dpaola2/Harmony/enclosure/mark-6/fit-rev-b/slicing/README.md

# Revision B prepared print plates

Print the wheel-check plate first. All plates use the A1, a 0.4 mm nozzle, PLA Basic and Textured PEI.

| Plate | Contents | Estimate |
| --- | --- | --- |
| [wheel-check](wheel-check/harmony-m6-b-wheel-check-a1.3mf) | Wheel coupon, four 14 mm spacers and pilot coupon | 27.4 minutes; 7.84 g |
| [shells](shells/harmony-m6-b-shells-a1.3mf) | Replacement tray and front | 98.1 minutes; 66.56 g |
| [retainers](retainers/harmony-m6-b-retainers-a1.3mf) | Two left and two right display retainers | 10.5 minutes; 0.8 g |

Print at 100% scale. Settings use 0.20 mm layers, four walls, 15% gyroid and no supports. The first plate has six objects.

The source STL hashes match the sliced inputs. Project G-code matches the standalone G-code. Mesh and deposited-path checks pass. Physical fit remains unverified.

Read the [assembly plan](../README.md) before assembling. The shells wait for the wheel test. Confirm loaded material and plate before printing. No printer job was sent.
