dpaola2/Harmony/PLAN.md

You can get *really* far on the software side before you ever touch a soldering iron or 3D printer, as long as you structure things right.

See `docs/README.md` for the documentation map and where to put gameplans vs. archives.

Given our MP3 player plan (ESP32, MicroPython, tactile buttons + small screen, Bluetooth audio out, iPod-style UI), here’s how I’d do it.

---

## Big idea: separate “brain” from “fingers”

Think in two layers:

1. **Core app logic (the “brain”)**

   * Knows:

     * What tracks exist
     * Which one is selected/playing
     * Current screen (Now Playing, Library, Settings, etc.)
     * How button presses change state
   * Doesn’t know:

     * What hardware it’s running on
     * Whether “up” came from a GPIO pin, a keyboard key, or a test

2. **Hardware layer (the “fingers”)**

   * Concrete implementations for:

     * Buttons
     * Screen
     * Storage (SD card / flash filesystem)
     * Audio/Bluetooth

If you design the core so it talks only to abstract interfaces (“give me button events”, “draw this text”), you can:

* Run everything on your laptop with **regular Python** and keyboard input.
* Write **unit tests** against the core.
* Only later write a MicroPython hardware adapter that plugs into the same interfaces.

---

## Phase 1 – Define your core interfaces & states

On your laptop, in a normal Python project:

1. **Define events**

   ```python
   from enum import Enum, auto

   class ButtonEvent(Enum):
       UP = auto()
       DOWN = auto()
       LEFT = auto()
       RIGHT = auto()
       SELECT = auto()
       BACK = auto()
       PLAY_PAUSE = auto()
   ```

2. **Define a minimal “screen” API**
   (this will be implemented differently on the laptop vs ESP32)

   ```python
   class Screen:
       def clear(self):
           raise NotImplementedError

       def draw_text(self, x: int, y: int, text: str):
           raise NotImplementedError

       def refresh(self):
           raise NotImplementedError
   ```

3. **Define a player model**

   ```python
   from dataclasses import dataclass

   @dataclass
   class Track:
       id: str
       title: str
       artist: str
       duration_secs: int
       path: str  # local file path

   @dataclass
   class PlayerState:
       tracks: list[Track]
       selected_index: int = 0
       playing_index: int | None = None
       is_playing: bool = False
       current_screen: str = "library"  # or "now_playing", "settings"
   ```

4. **Define core commands the hardware will call**

   ```python
   class PlayerApp:
       def __init__(self, state: PlayerState, screen: Screen):
           self.state = state
           self.screen = screen

       def handle_button(self, event: ButtonEvent):
           # purely state transitions; no GPIO, no Bluetooth here
           if self.state.current_screen == "library":
               self._handle_library_input(event)
           elif self.state.current_screen == "now_playing":
               self._handle_now_playing_input(event)
           self.render()

       def render(self):
           # draw the current UI to the screen abstraction
           self.screen.clear()
           if self.state.current_screen == "library":
               self._render_library()
           elif self.state.current_screen == "now_playing":
               self._render_now_playing()
           self.screen.refresh()
   ```

All of this is **100% portable** between your laptop and the ESP32.

---

## Phase 2 – Build a PC “simulator” (your first working app)

Now you make a fake hardware layer that runs on your laptop:

1. **Text-based screen implementation**
   Example: use `curses` or just simple print-based rendering.

   ```python
   import os

   class ConsoleScreen(Screen):
       def clear(self):
           os.system("clear")

       def draw_text(self, x: int, y: int, text: str):
           # simplest version: ignore x,y and just print lines
           print(text)

       def refresh(self):
           pass
   ```

2. **Keyboard → button events**

   * For a quick prototype, just read input from the keyboard in a loop:

     ```python
     key_map = {
         "w": ButtonEvent.UP,
         "s": ButtonEvent.DOWN,
         "a": ButtonEvent.LEFT,
         "d": ButtonEvent.RIGHT,
         " ": ButtonEvent.SELECT,
         "p": ButtonEvent.PLAY_PAUSE,
         "q": ButtonEvent.BACK,
     }
     ```

3. **Run loop**

   ```python
   def main():
       tracks = [
           Track("1", "Song One", "Artist A", 180, "/music/song1.mp3"),
           Track("2", "Song Two", "Artist B", 200, "/music/song2.mp3"),
       ]
       state = PlayerState(tracks=tracks)
       screen = ConsoleScreen()
       app = PlayerApp(state, screen)

       app.render()
       while True:
           key = input("Key (w/s/a/d/space/p/q): ").strip()
           if key == "x":
               break
           event = key_map.get(key)
           if event:
               app.handle_button(event)

   if __name__ == "__main__":
       main()
   ```

At this point you’ll have:

* A working “MP3 player” UI on your laptop
* Library navigation
* Now Playing screen
* Play/pause state machine (even if audio is stubbed)

---

## Phase 3 – Add tests around the core

Now that your logic is decoupled, you can test it like a normal app:

1. **Install pytest** and write tests:

   ```python
   def test_down_moves_selection():
       tracks = [Track(str(i), f"Song {i}", "Artist", 120, "") for i in range(3)]
       state = PlayerState(tracks=tracks)
       screen = DummyScreen()  # no-op implementation

       app = PlayerApp(state, screen)
       app.handle_button(ButtonEvent.DOWN)
       assert app.state.selected_index == 1
   ```

2. Test scenarios like:

   * Pressing PLAY on Library → sets `playing_index` and `is_playing = True`
   * Pressing PLAY on Now Playing toggles pause
   * Reaching end of list wraps or stops (decide behavior)
   * BACK from Now Playing returns you to Library

These tests are the safety net you’ll keep using when you later port to MicroPython.

---

## Phase 4 – Decide how “real” audio works

You can keep audio out of the core and treat it as a **service**:

```python
class AudioBackend:
    def play(self, track: Track): ...
    def pause(self): ...
    def resume(self): ...
    def stop(self): ...
```

* In your **PC simulator**, `AudioBackend` could:

  * Actually play MP3s using a Python library, **or**
  * Just print what it *would* do (“Playing Song One”).
* On the **ESP32**, `AudioBackend` becomes:

  * A MicroPython module that:

    * Reads from SD card/flash
    * Sends PCM over I2S to a DAC/headphone amp **or**
    * Streams via Bluetooth A2DP (harder but doable in C/ESP-IDF; MicroPython options are more limited).

Your core `PlayerApp` just calls:

```python
def _play_selected_track(self):
    track = self.state.tracks[self.state.selected_index]
    self.audio_backend.play(track)
    self.state.playing_index = self.state.selected_index
    self.state.is_playing = True
```

---

## Phase 5 – Only then worry about actual hardware

When your laptop simulator feels good and tests are passing, *then* you start working with an ESP32 dev board:

1. **Pick an ESP32 dev board + display** (this was in our other chat).
2. **Port the core to MicroPython**:

   * Most of your Python code will just work.
   * You might have to trim things for memory and avoid heavy libraries.
3. **Implement MicroPython versions of your interfaces**:

   * `EspScreen` using your actual display driver.
   * `EspButtons` that reads GPIOs and maps them to `ButtonEvent`s.
   * `EspAudioBackend` that hooks into whatever audio path you choose.

Because the interfaces are already defined, this becomes “just wiring”:

```python
# micropython_main.py
from core import PlayerApp, PlayerState, Track, ButtonEvent
from esp_screen import EspScreen
from esp_buttons import read_button_event
from esp_audio import EspAudioBackend

def main():
    tracks = load_tracks_from_fs()  # same idea as on PC
    state = PlayerState(tracks=tracks)
    screen = EspScreen()
    audio = EspAudioBackend()
    app = PlayerApp(state, screen, audio_backend=audio)

    app.render()
    while True:
        event = read_button_event()
        if event:
            app.handle_button(event)
```

You’ll still test logic changes on your PC first, run pytest, then deploy to the ESP32 dev board to verify hardware behavior.

---

## Phase 6 – Only *after* that: custom PCB + 3D case

Once:

* The app feels good in the simulator
* The ESP32 dev board version works reliably
* You’re comfortable with button layout and screen usage

**Then** you:

* Lock in hardware choices (exact ESP32 module, DAC, amp, battery management).
* Design PCB + mechanical layout.
* Design and 3D-print the case around that.

At that point you’re mostly doing **mechanical integration**, not discovering fundamental UI or software architecture issues.

---

## If you want, next step

If you’d like, I can:

* Turn this into a **repo structure** (folder layout, file names, `core/`, `platform/pc/`, `platform/esp32/`, etc.), and
* Sketch a minimal but real `PlayerApp` and a couple of pytest tests you could literally drop into a new project.
