dpaola2/Harmony/enclosure/harmony-r1/preview/exploded.png

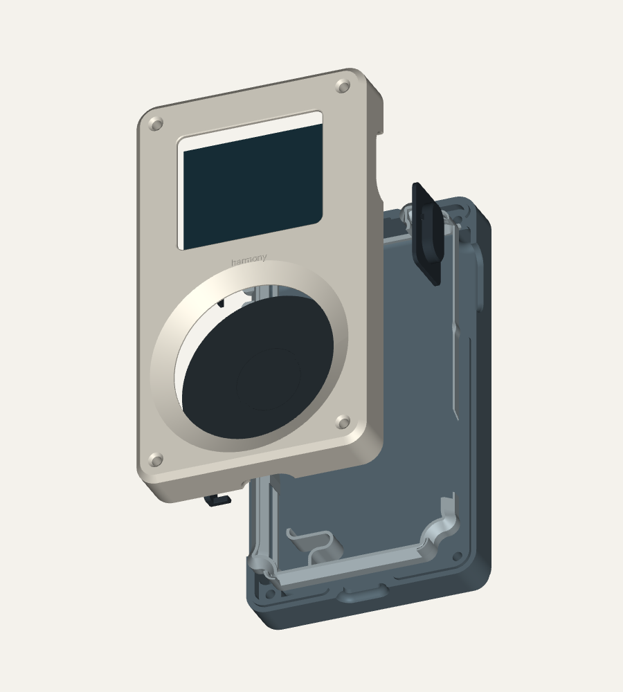
enclosure/harmony-r1/preview/exploded.png
