dpaola2/Harmony/enclosure/harmony-r2-globtek/preview/globtek-fit.png

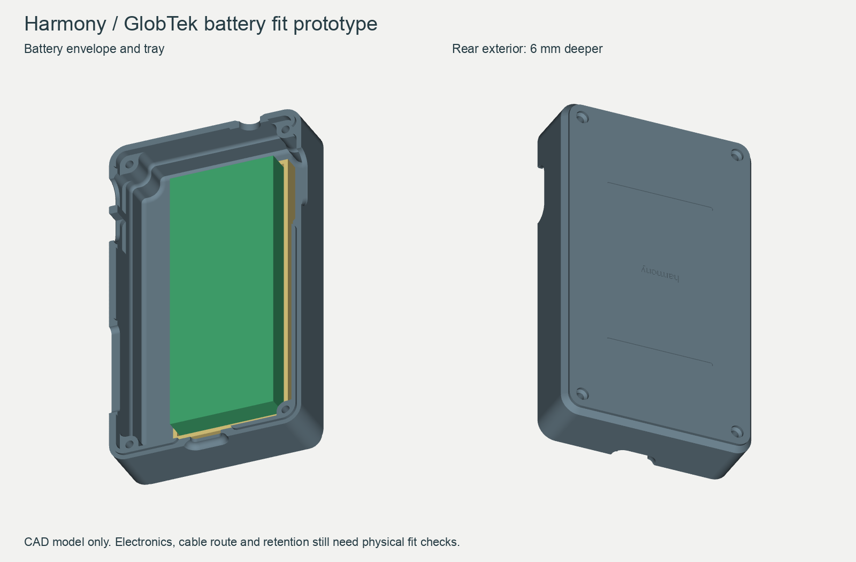
enclosure/harmony-r2-globtek/preview/globtek-fit.png
