dpaola2/Harmony/enclosure/harmony-r2-globtek/preview/inside.png

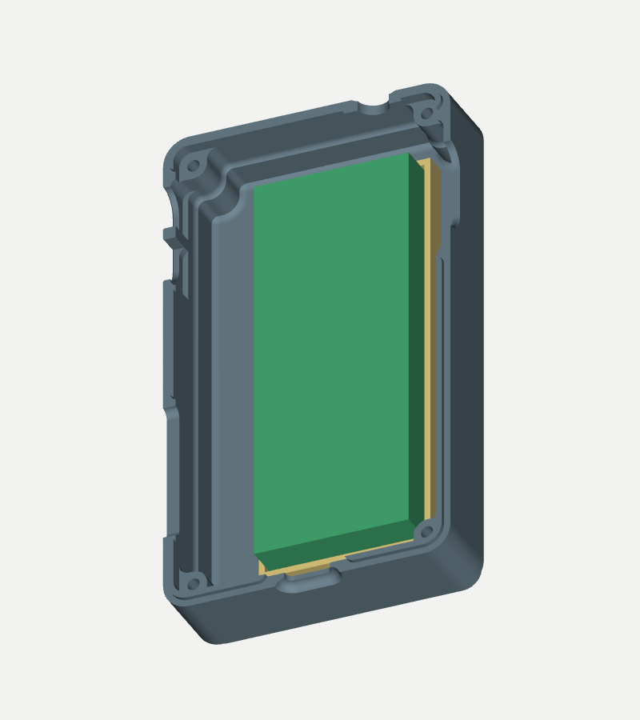
enclosure/harmony-r2-globtek/preview/inside.png
