dpaola2/Harmony/enclosure/harmony-r2-globtek/preview/outside.png

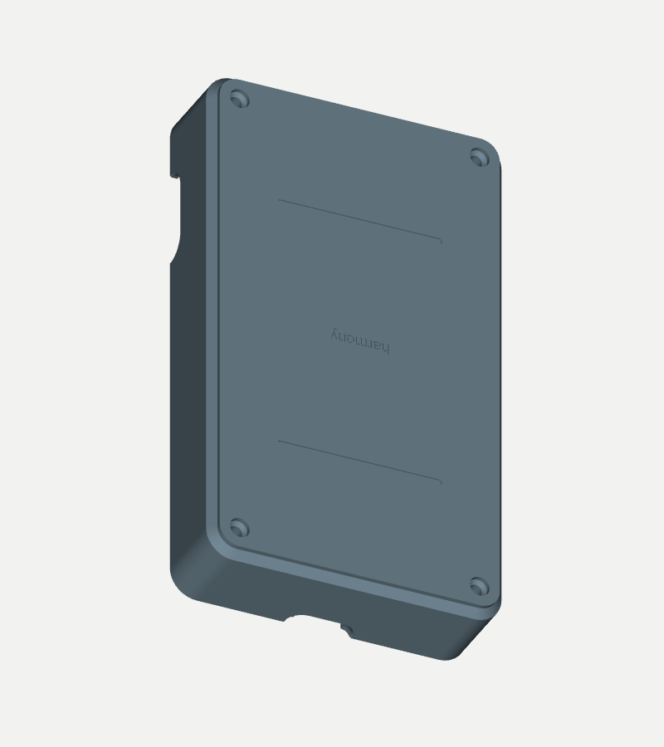
enclosure/harmony-r2-globtek/preview/outside.png
