dpaola2/Harmony/enclosure/mark-6/fit-prototype/preview/hollow-fit.png

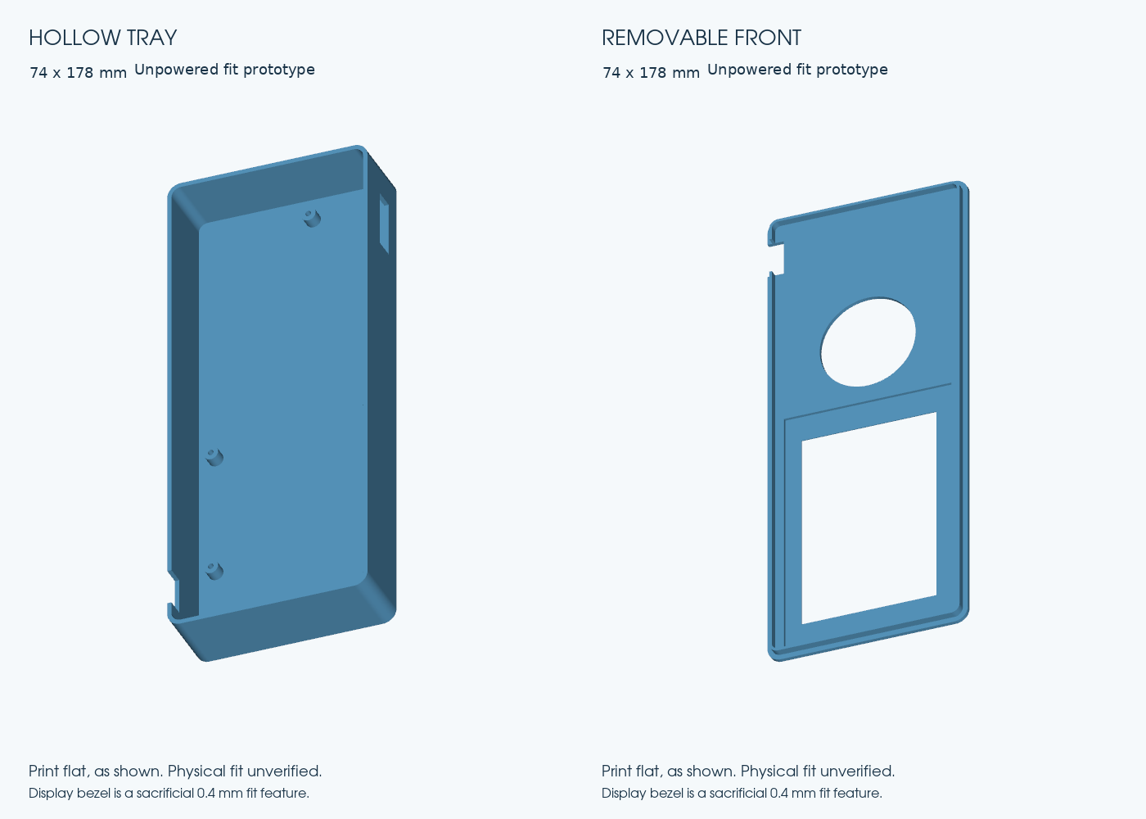
enclosure/mark-6/fit-prototype/preview/hollow-fit.png
