dpaola2/Harmony/enclosure/mark-6/fit-rev-b/slicing/retainers/toolpath-review.png

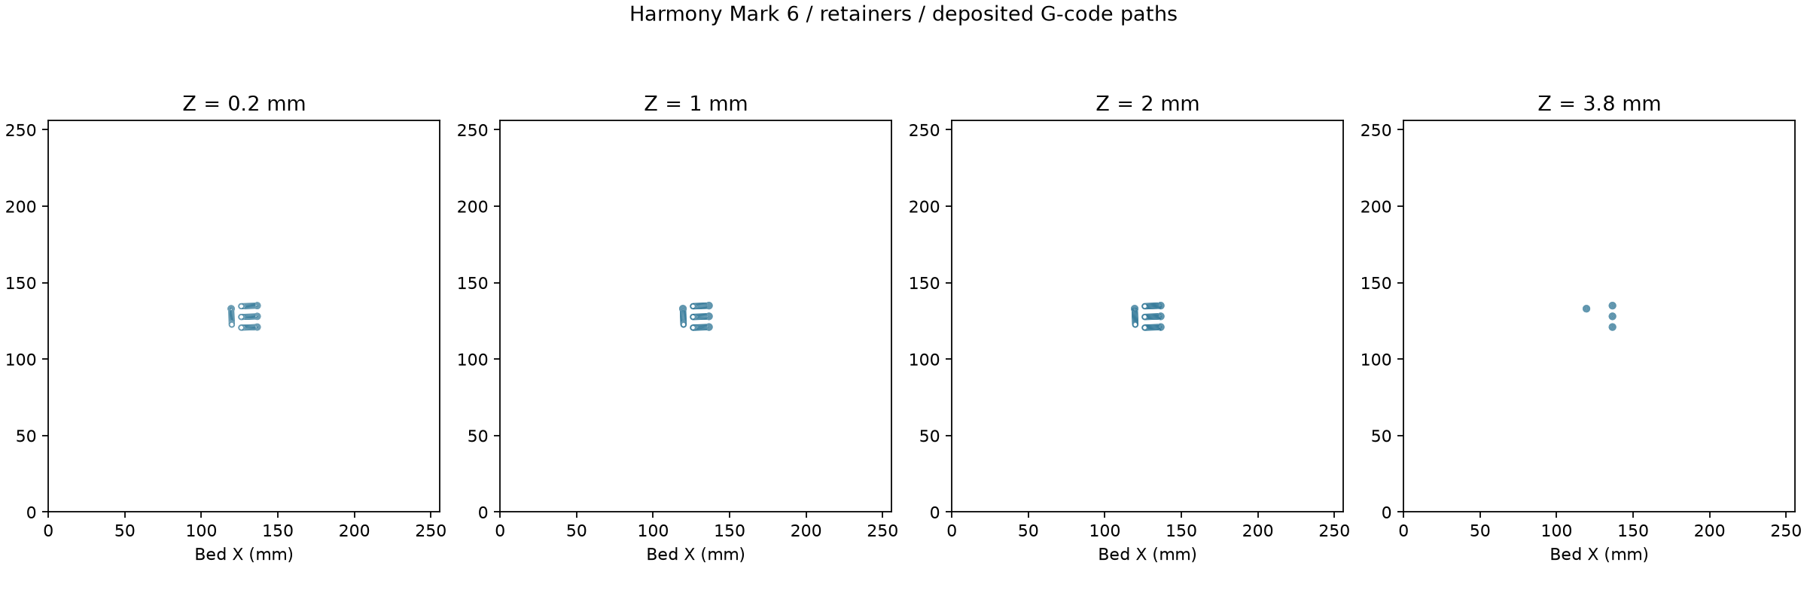
enclosure/mark-6/fit-rev-b/slicing/retainers/toolpath-review.png
