dpaola2/Harmony/enclosure/mark-6/fit-rev-b/slicing/shells/toolpath-review.png

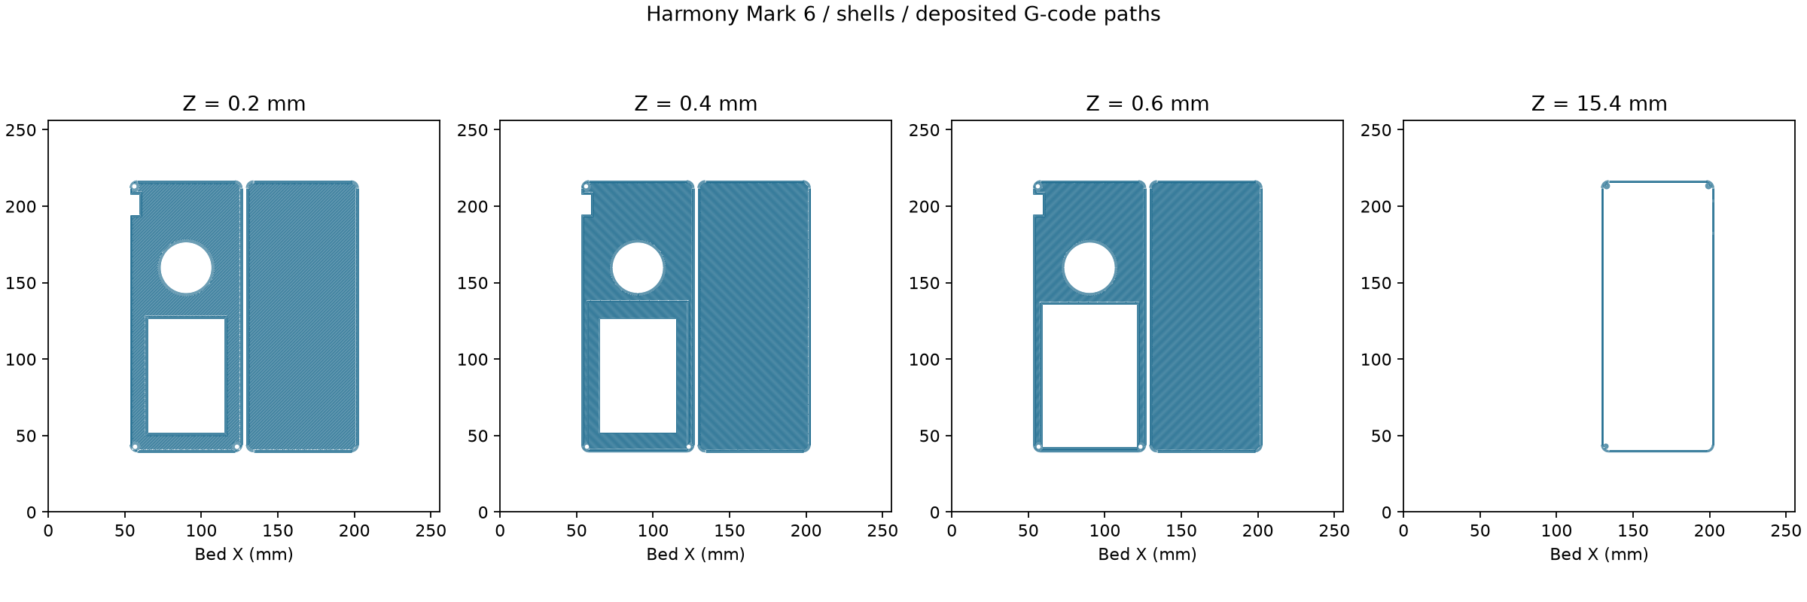
enclosure/mark-6/fit-rev-b/slicing/shells/toolpath-review.png
