dpaola2/Harmony/enclosure/mark-6/size-mockup/preview/size-mockup.png

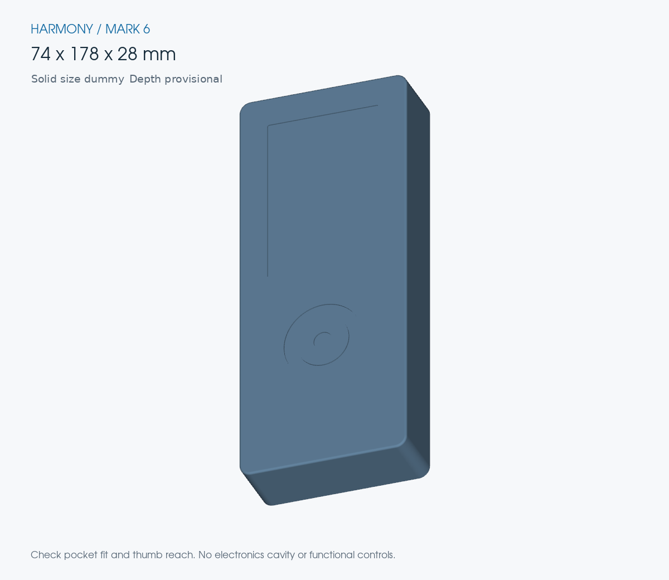
enclosure/mark-6/size-mockup/preview/size-mockup.png
