dpaola2/Harmony/hardware/mark-7/inventory-20260928/README.md

# September 28 Mark-7 inventory evidence

Dave supplied these original photographs during scope definition.

- `IMG_7727.HEIC`: GlobTek BL2200F9031781S1PCKT, 3.7 V, 2200 mAh, 8.14 Wh. Label assigns red positive, white NTC and black negative. Connector voltage and polarity remain unmeasured.
- `IMG_7730.HEIC`: ELEGOO Double Sided PCB Kit packaging. It advertises plated holes, five board sizes and 1.6 mm FR4. The contents, exact dimensions and pad connectivity remain unmeasured.

Dave reports ample wire, a multimeter and a soldering iron. He reports purchasing Adafruit #4046, #261 and #4559. These statements establish inventory and purchase intent/results, not an assembled or electrically verified adapter.

Original file checksums are in `sha256.json`. See [portable scope](../../../docs/mark-7-portable-scope.md) and [Mark-6 lessons](../../../docs/mark-6-lessons-and-portable-next-step.md). Build Mark-7 portable Bluetooth player (HARMONY-19) owns follow-up work.
