dpaola2/Harmony/hardware/mark-6/carrier-rev-a/output/supplier-quote/supplier-request-draft.md

# Mark 6 supplier request draft

Prepared September 26, 2026. Unsent. Proposed recipient: service@pcbway.com.
Attachment: `harmony-mark6-rev-a-supplier-quote.zip`.

Subject: DFM review and turnkey quote: Harmony Mark 6 carrier, Rev A

Hello,

Please quote fabrication and complete assembly of the attached four-layer carrier. Please price one, two and five assembled carriers separately. Your website lists a five-piece minimum. If that applies here, please distinguish the minimum bare-board quantity from the minimum assembled quantity.

Each carrier has 36 installed components: 34 SMT parts and two through-hole Samtec sockets. Please source the exact BOM and install both sockets. The customer must receive a carrier that requires no soldering. External processor, display and control modules are outside this quote.

The board needs 1.6 mm FR-4, ENIG and resin-filled, copper-capped vias at the nine listed locations. Please preserve the antenna cutout and copper exclusion. The package includes fabrication details and connector constraints.

Please return the DFM findings, BOM availability, proposed stackup, panel drawing and placement preview. Review U1's stencil and thermal holes, socket tail tolerances, and connector orientation. Identify substitutions for approval before using them.

Please itemize boards, components, assembly, tooling, testing and shipping to the United States. Include minimum component quantities, unused-part policy, lead time, quote validity and tax or duty assumptions. State any holiday effect on the schedule.

This request is for review and pricing only. Please wait for written production release before fabrication or assembly. Header mating, ribbon mapping and powered qualification remain open.

Thank you,
Dave
