dpaola2/Harmony/enclosure/mark-6/fit-prototype/cad/ano-spacer-12mm.step

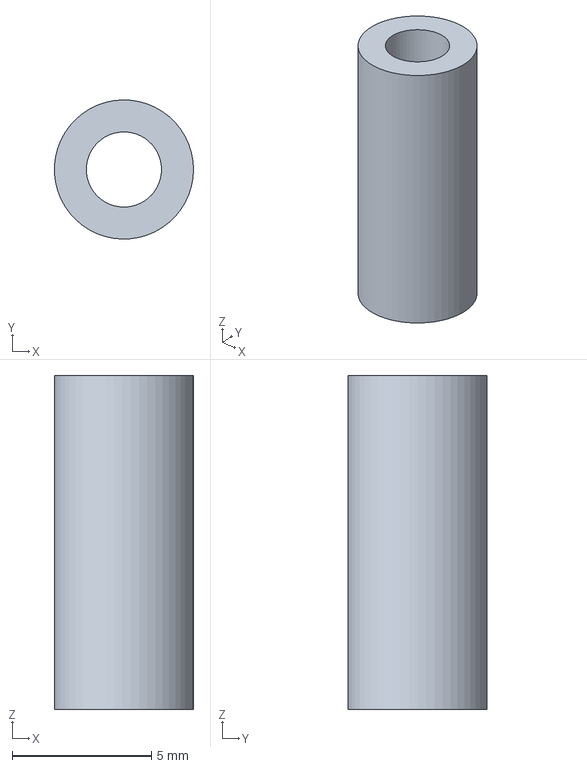
[picture p33: CAD file, 2026-09-25]
enclosure/mark-6/fit-prototype/cad/ano-spacer-12mm.step
5.00 x 5.00 x 12.0 mm
