dpaola2/Harmony/enclosure/mark-6/fit-prototype/slicing/gauges/harmony-mark6-gauges-a1.3mf

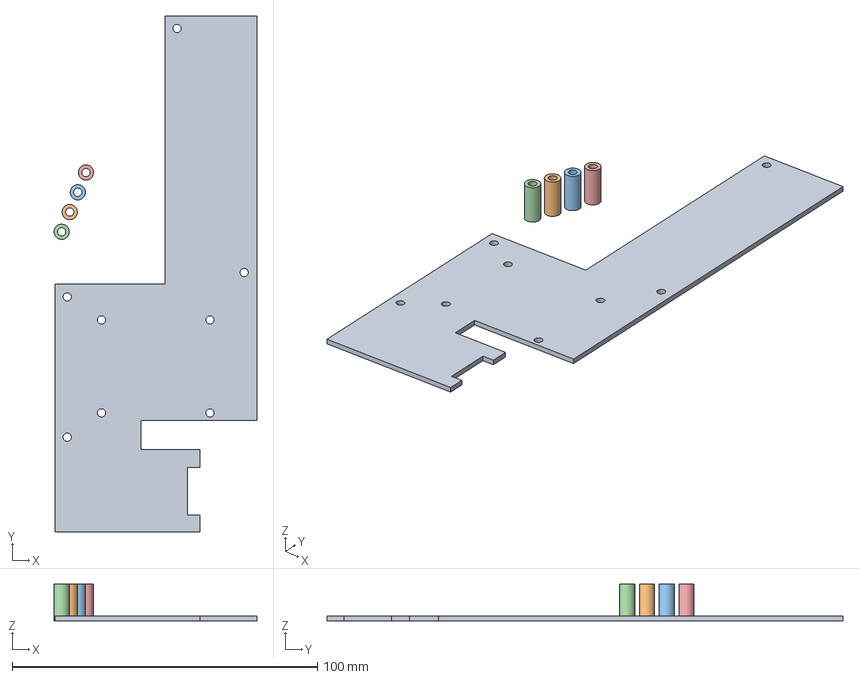
[picture p34: CAD file, 2026-09-25]
enclosure/mark-6/fit-prototype/slicing/gauges/harmony-mark6-gauges-a1.3mf
66.5 x 169.0 x 12.0 mm
harmony-mark6-carrier-gauge.stl
harmony-mark6-ano-spacer-12mm.stl_1
harmony-mark6-ano-spacer-12mm.stl_2
harmony-mark6-ano-spacer-12mm.stl_3
harmony-mark6-ano-spacer-12mm.stl_4
