dpaola2/Harmony/enclosure/mark-6/fit-prototype/slicing/shells/harmony-mark6-shells-a1.3mf

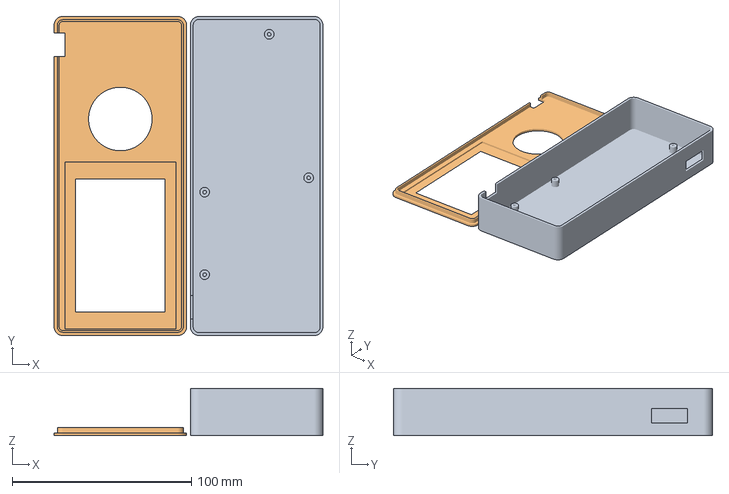
[picture p35: CAD file, 2026-09-25]
enclosure/mark-6/fit-prototype/slicing/shells/harmony-mark6-shells-a1.3mf
150.0 x 178.0 x 26.4 mm
harmony-mark6-tray.stl
harmony-mark6-front.stl
