dpaola2/Harmony/enclosure/mark-6/fit-rev-b/slicing/retainers/harmony-m6-b-retainers-a1.3mf

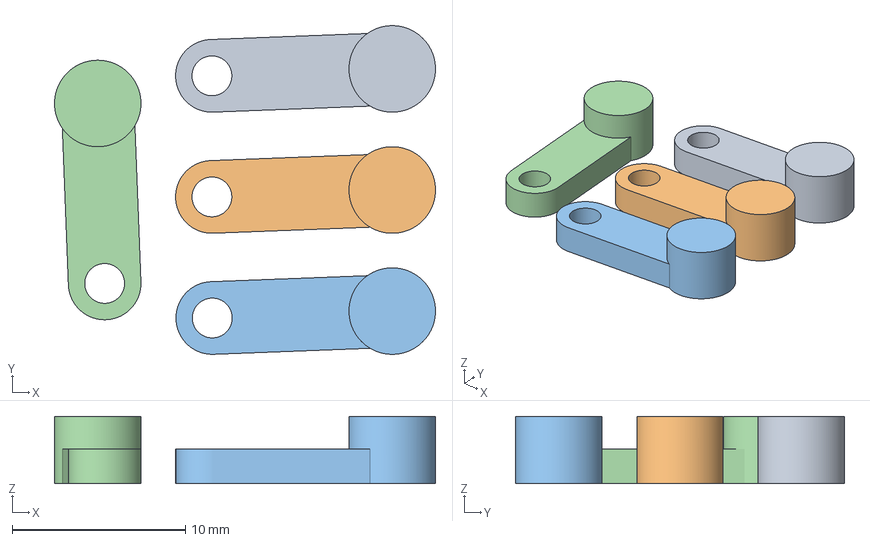
[picture p36: CAD file, 2026-09-26]
enclosure/mark-6/fit-rev-b/slicing/retainers/harmony-m6-b-retainers-a1.3mf
22.0 x 19.0 x 3.90 mm
harmony-m6-b-display-retainer-left.stl_1
harmony-m6-b-display-retainer-left.stl_2
harmony-m6-b-display-retainer-right.stl_1
harmony-m6-b-display-retainer-right.stl_2
