dpaola2/Harmony/enclosure/mark-6/fit-rev-b/slicing/shells/harmony-m6-b-shells-a1.3mf

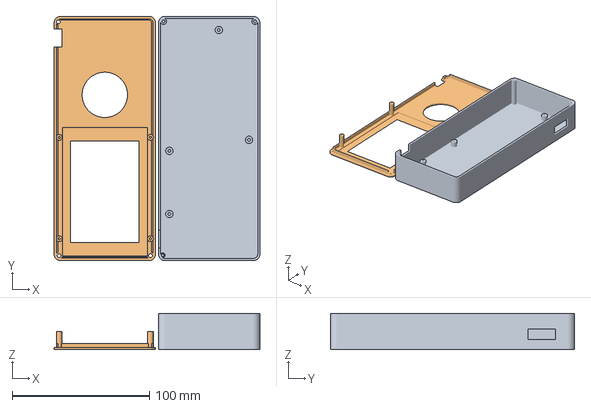
[picture p37: CAD file, 2026-09-26]
enclosure/mark-6/fit-rev-b/slicing/shells/harmony-m6-b-shells-a1.3mf
150.0 x 178.0 x 26.4 mm
harmony-m6-b-tray.stl
harmony-m6-b-front.stl
