dpaola2/Harmony/enclosure/mark-6/fit-rev-b/slicing/wheel-check/harmony-m6-b-wheel-check-a1.3mf

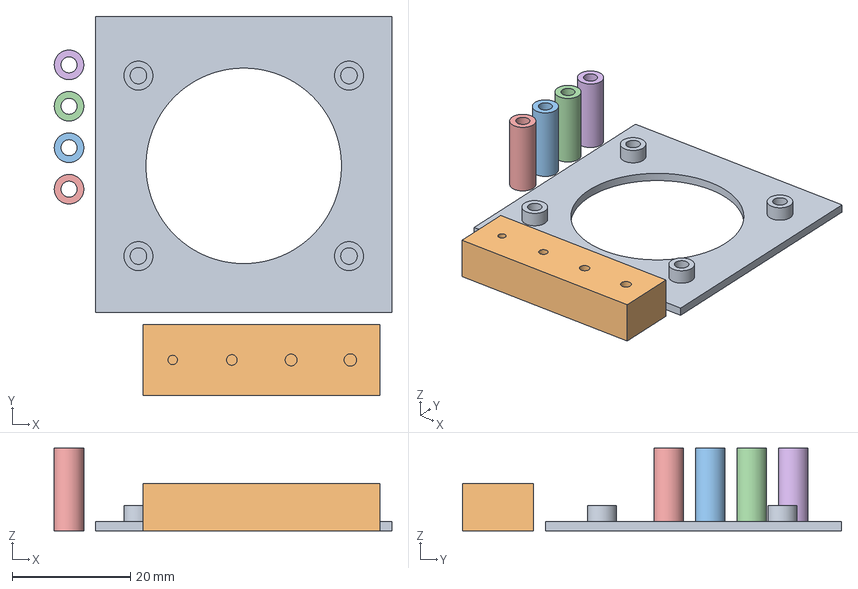
[picture p38: CAD file, 2026-09-26]
enclosure/mark-6/fit-rev-b/slicing/wheel-check/harmony-m6-b-wheel-check-a1.3mf
57.0 x 64.0 x 14.0 mm
harmony-m6-b-wheel-coupon.stl
harmony-m6-b-pilot-coupon.stl
harmony-m6-b-ano-spacer-14mm.stl_1
harmony-m6-b-ano-spacer-14mm.stl_2
harmony-m6-b-ano-spacer-14mm.stl_3
harmony-m6-b-ano-spacer-14mm.stl_4
