dpaola2/Harmony/enclosure/mark-6/size-mockup/cad/harmony-mark6-size.step

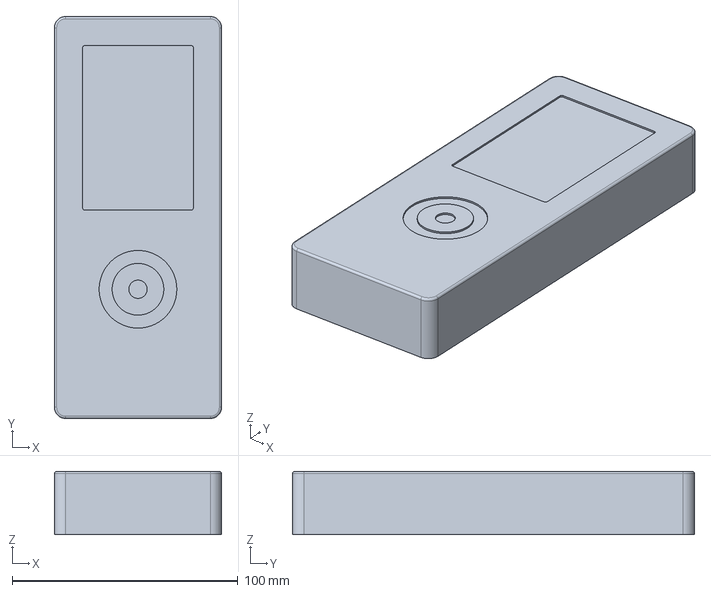
[picture p39: CAD file, 2026-09-25]
enclosure/mark-6/size-mockup/cad/harmony-mark6-size.step
74.0 x 178.0 x 28.0 mm
