dpaola2/Harmony/enclosure/harmony-r1/cad/battery-envelope-reference.step

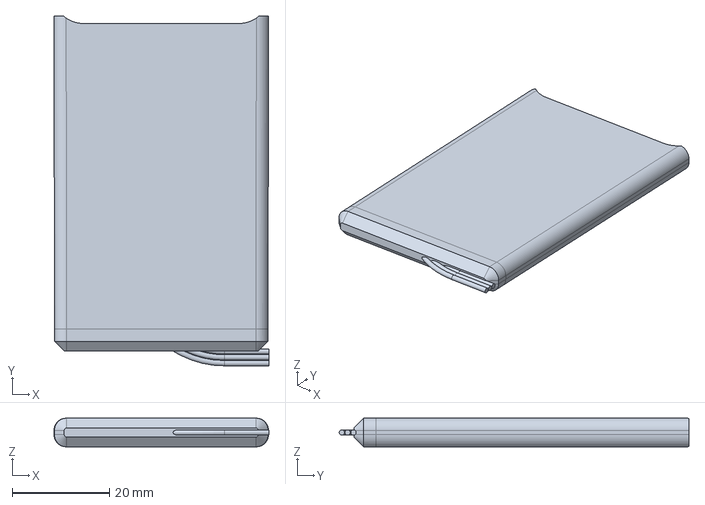
[picture p40: CAD file, 2026-09-20]
enclosure/harmony-r1/cad/battery-envelope-reference.step
44.3 x 72.1 x 5.90 mm
