dpaola2/Harmony/enclosure/harmony-r1/print/harmony-fit-test.3mf

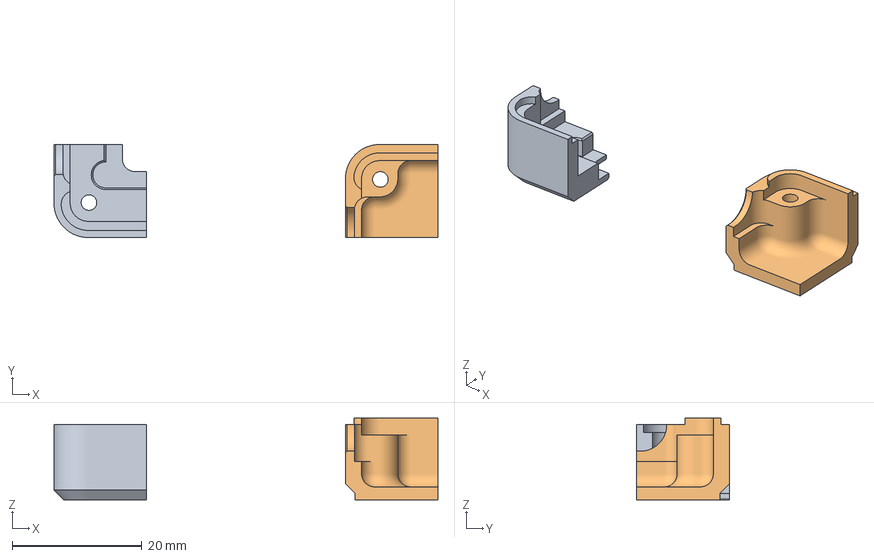
[picture p41: CAD file, 2026-09-20]
enclosure/harmony-r1/print/harmony-fit-test.3mf
59.3 x 14.4 x 12.6 mm
fit-front
fit-back
