dpaola2/Harmony/enclosure/harmony-r1/source/Case.FCStd

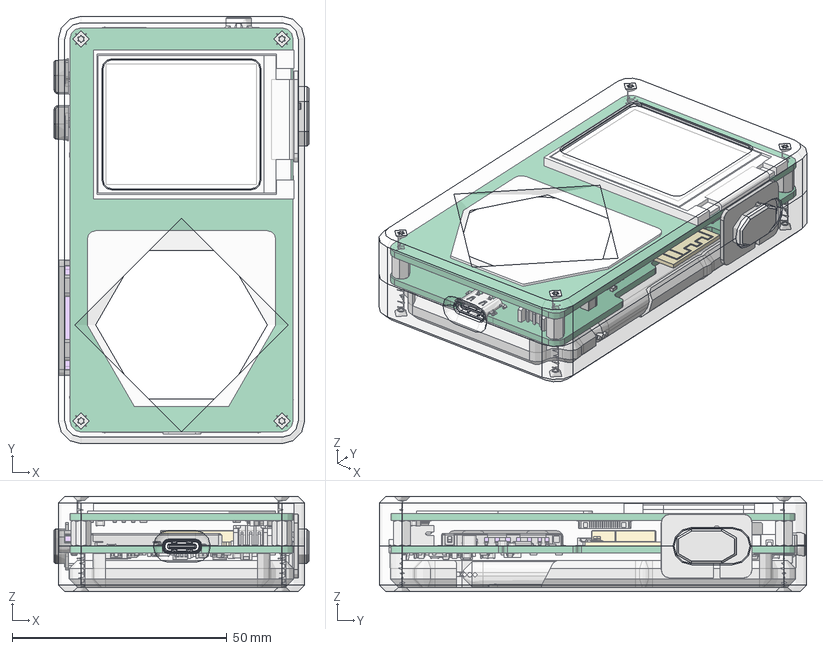
[picture p42: CAD file, 2026-09-20]
enclosure/harmony-r1/source/Case.FCStd
59.4 x 99.6 x 22.2 mm
Back
Pcb_d9b2
${REFERENCE}_TSOT_23_null
${REFERENCE}_SOT_23_5_null
${REFERENCE}_L_1008_2520Metric_null x 2
${REFERENCE}_R_0805_2012Metric_null x 4
${REFERENCE}_C_0805_2012Metric_null x 16
${REFERENCE}_R_0603_1608Metric_null x 28
${REFERENCE}_QFN-20-1EP_4x4mm_Pitch0.5mm_null
${REFERENCE}_C_0603_1608Metric_null x 11
${REFERENCE}_HVQFN_24_1EP_4x4mm_P05mm_EP21x21mm_null
${REFERENCE}_SOT_23_null
${REFERENCE}_SOT_323_SC_70_null x 2
REF_WSON-10-1EP_2.5x2.5mm_P0.5mm_EP1.2x2mm_null
${REFERENCE}_SOT_23_6_null
${REFERENCE}_C_1206_3216Metric_null x 3
${REFERENCE}_SSOP_20_44x65mm_P065mm_null
${REFERENCE}_TQFP_32_7x7mm_P08mm_null
U7_WSON8_4x4mm_Pitch08mm_null
PCB Edge_usb4510-03-1-a_null
${REFERENCE}_L_0603_1608Metric_null
${REFERENCE}_JST_S3B_PH_K_null
J2_5052781533_null
${REFERENCE}_TSSOP_16_44x5mm_P065mm_null
${REFERENCE}_microSD_HC_Hirose_DM3D-SF_null[2]
${REFERENCE}_DM1AA-SF-PEJ v2_null[3]
PCB EDGE_EVQ-P4HB3B--3DModel-STEP-56544_null x 2
U15_ESP32-WROVER-I--3DModel-STEP-56544_null[2]
${REFERENCE}_JS102011SAQN v2_null
${REFERENCE}_C_1210_3225Metric_null
PCB EDGE_SJ-3506-SMT_null
Pcb_8c068
${REFERENCE}_R_0603_1608Metric_null028 x 9
${REFERENCE}_C_0805_2012Metric_null016 x 3
${REFERENCE}_C_1206_3216Metric_null003
J4_5052781533_null
${REFERENCE}_VSSOP_10_3x3mm_P05mm_null
${REFERENCE}_C_0603_1608Metric_null011
${REFERENCE}_SOT_323_SC_70_null002
Touchpad (Smaller)
Display (ER-TFT018-2)
Wurth 970060244 (Top Left)
Wurth 970060244 (Top Right)
Wurth 970060244 (Bottom Left)
Wurth 970060244 (Bottom Right)
474283-SHK-M2-8-V2-A2 (Top Left)
474283-SHK-M2-8-V2-A2 (Top Right)
474283-SHK-M2-8-V2-A2 (Bottom Left)
474283-SHK-M2-8-V2-A2 (Bottom Right)
474289-SHK-M2-8-V2-A2 (Top Left)
474289-SHK-M2-8-V2-A2 (Top Right)
474289-SHK-M2-8-V2-A2 (Bottom Left)
474289-SHK-M2-8-V2-A2 (Bottom Right)
SD Card Blank
Battery (Batch 0, Smaller)
Battery (Batch 1, Larger)
Button1
Button2
Switch
SD Caddy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
