dpaola2/Harmony/enclosure/harmony-r2-globtek/print/battery-dummy.stl

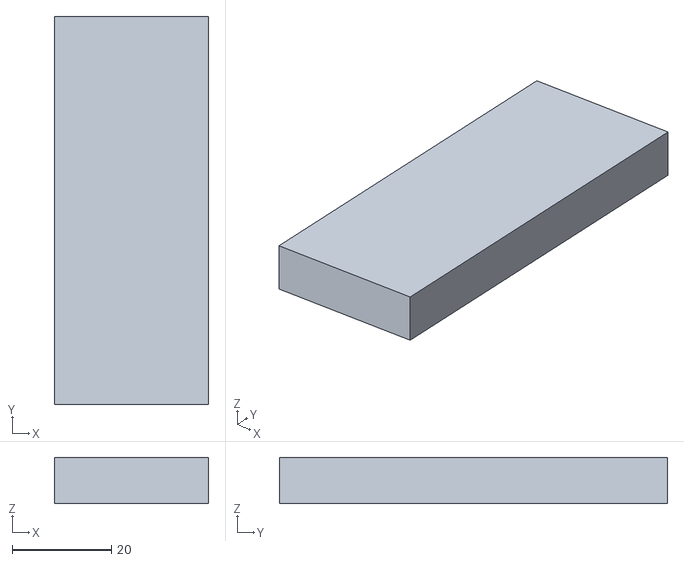
[picture p43: CAD file, 2026-09-20]
enclosure/harmony-r2-globtek/print/battery-dummy.stl
31.0 x 78.0 x 9.30
