dpaola2/Harmony/enclosure/mark-6/fit-prototype/print/harmony-mark6-front.3mf

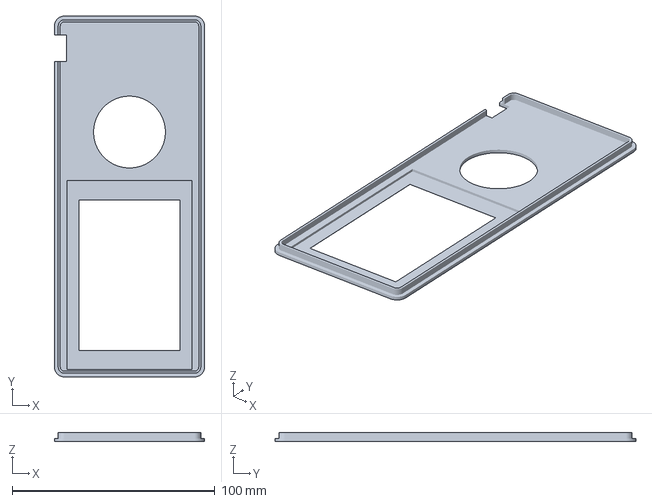
[picture p44: CAD file, 2026-09-25]
enclosure/mark-6/fit-prototype/print/harmony-mark6-front.3mf
74.0 x 178.0 x 4.60 mm
