dpaola2/Harmony/enclosure/mark-6/fit-rev-b/print/harmony-m6-b-pilot-coupon.3mf

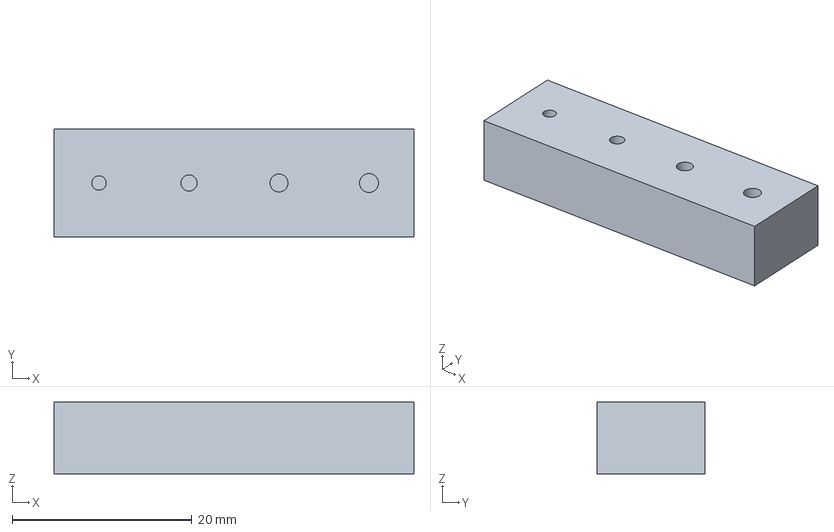
[picture p45: CAD file, 2026-09-26]
enclosure/mark-6/fit-rev-b/print/harmony-m6-b-pilot-coupon.3mf
40.0 x 12.0 x 8.00 mm
