dpaola2/Harmony/enclosure/harmony-r1/cad/display-lens-reference.step

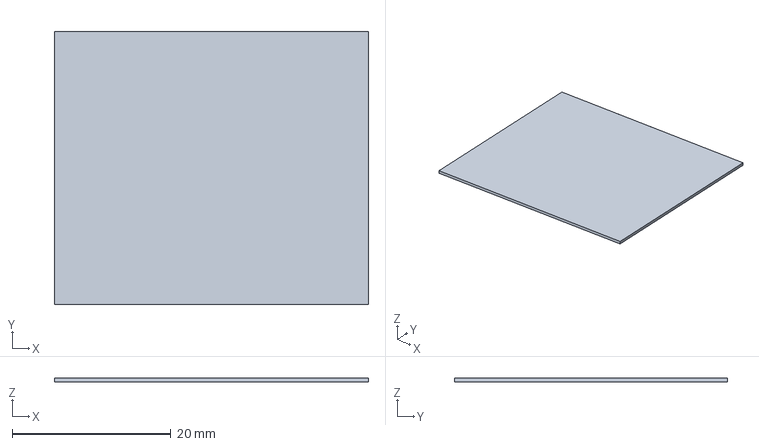
[picture p46: CAD file, 2026-09-20]
enclosure/harmony-r1/cad/display-lens-reference.step
39.6 x 34.4 x 0.5 mm
