dpaola2/Harmony/enclosure/harmony-r1/print/harmony-small-parts.3mf

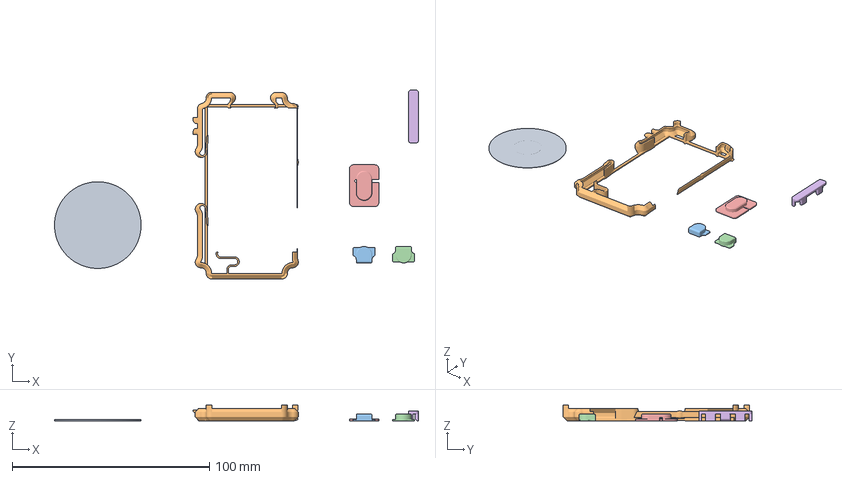
[picture p47: CAD file, 2026-09-20]
enclosure/harmony-r1/print/harmony-small-parts.3mf
184.5 x 95.8 x 7.90 mm
touch-cover
battery-cage
button-upper
button-lower
hold-switch
sd-caddy
