dpaola2/Harmony/enclosure/harmony-r2-globtek/cad/battery-clearance-envelope.step

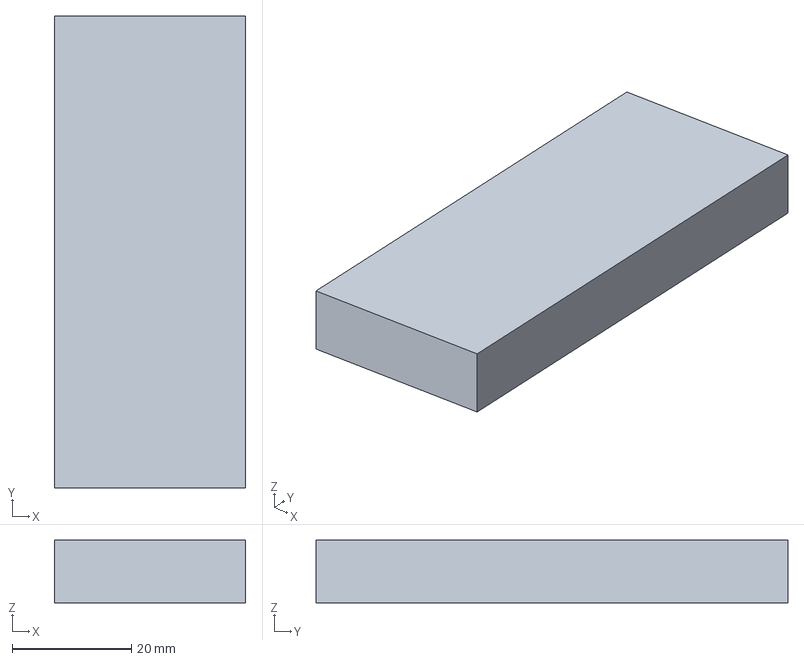
[picture p48: CAD file, 2026-09-20]
enclosure/harmony-r2-globtek/cad/battery-clearance-envelope.step
32.0 x 79.0 x 10.5 mm
