dpaola2/Harmony/enclosure/mark-6/fit-rev-b/cad/ano-spacer-14mm.step

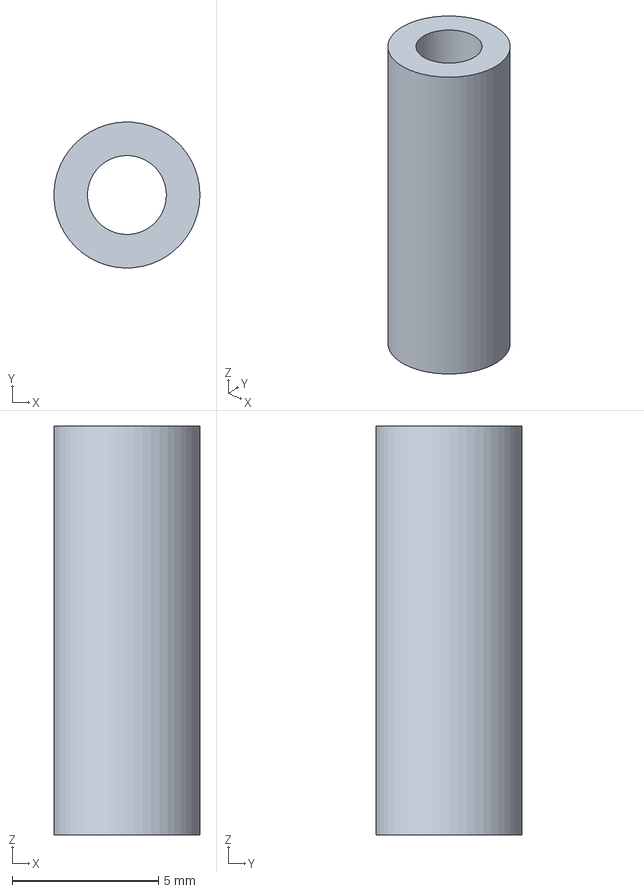
[picture p49: CAD file, 2026-09-26]
enclosure/mark-6/fit-rev-b/cad/ano-spacer-14mm.step
5.00 x 5.00 x 14.0 mm
