dpaola2/Harmony/enclosure/mark-6/fit-rev-b/print/harmony-m6-b-wheel-coupon.3mf

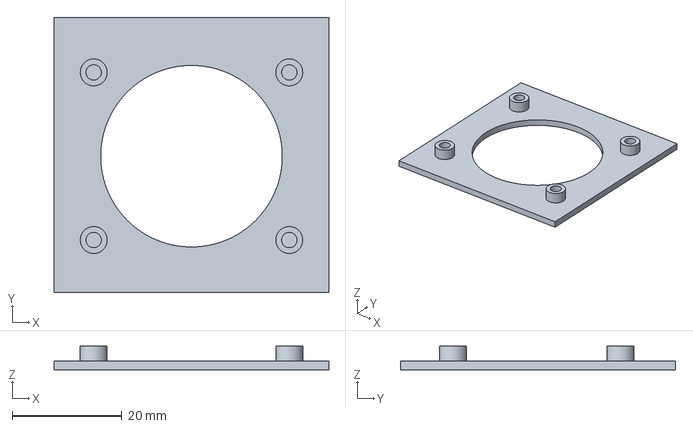
[picture p50: CAD file, 2026-09-26]
enclosure/mark-6/fit-rev-b/print/harmony-m6-b-wheel-coupon.3mf
50.0 x 50.0 x 4.33 mm
