dpaola2/Harmony/enclosure/harmony-r2-globtek/cad/back.step

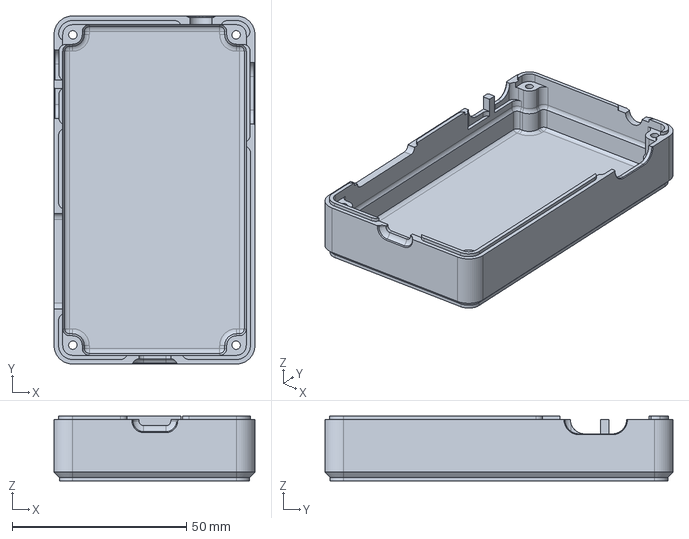
[picture p51: CAD file, 2026-09-20]
enclosure/harmony-r2-globtek/cad/back.step
57.6 x 99.8 x 18.6 mm
