dpaola2/Harmony/enclosure/harmony-r1/cad/battery-cage.step

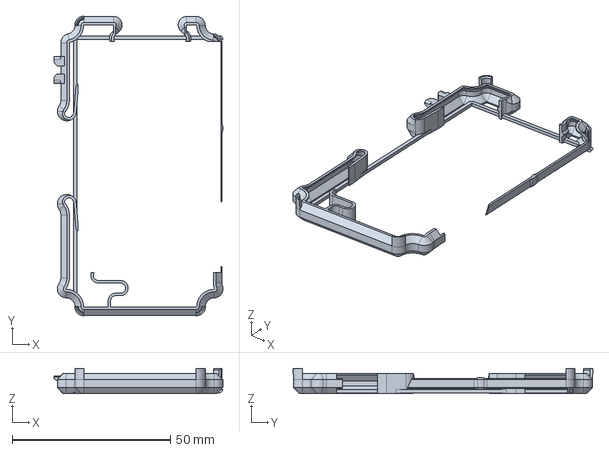
[picture p52: CAD file, 2026-09-20]
enclosure/harmony-r1/cad/battery-cage.step
53.3 x 94.7 x 7.90 mm
