dpaola2/Harmony/enclosure/harmony-r2-globtek/cad/touch-cover.step

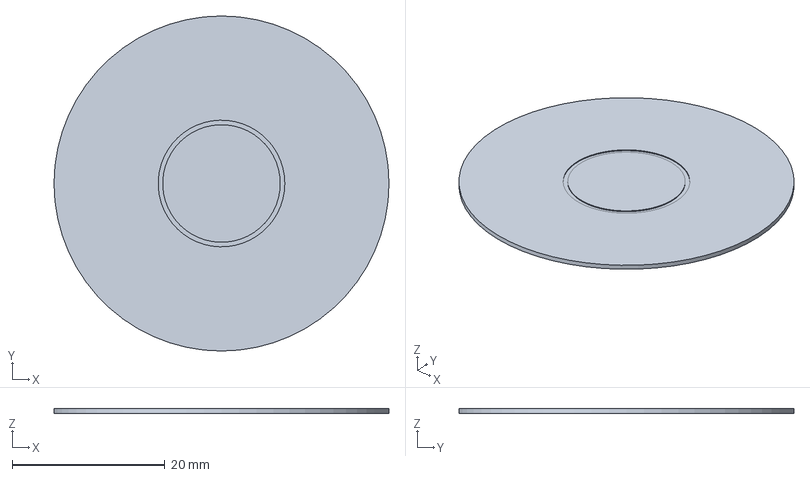
[picture p53: CAD file, 2026-09-20]
enclosure/harmony-r2-globtek/cad/touch-cover.step
43.9 x 43.9 x 0.6 mm
