dpaola2/Harmony/enclosure/harmony-r1/cad/back.step

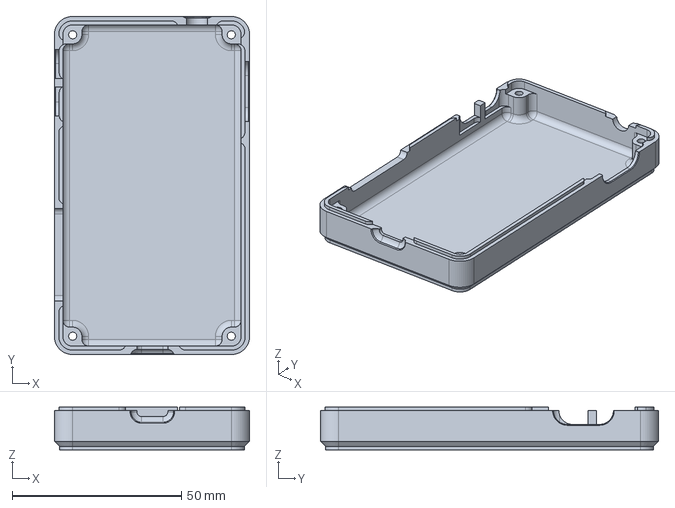
[picture p54: CAD file, 2026-09-20]
enclosure/harmony-r1/cad/back.step
57.6 x 99.8 x 12.6 mm
