dpaola2/Harmony/enclosure/harmony-r2-globtek/cad/battery-cage.step

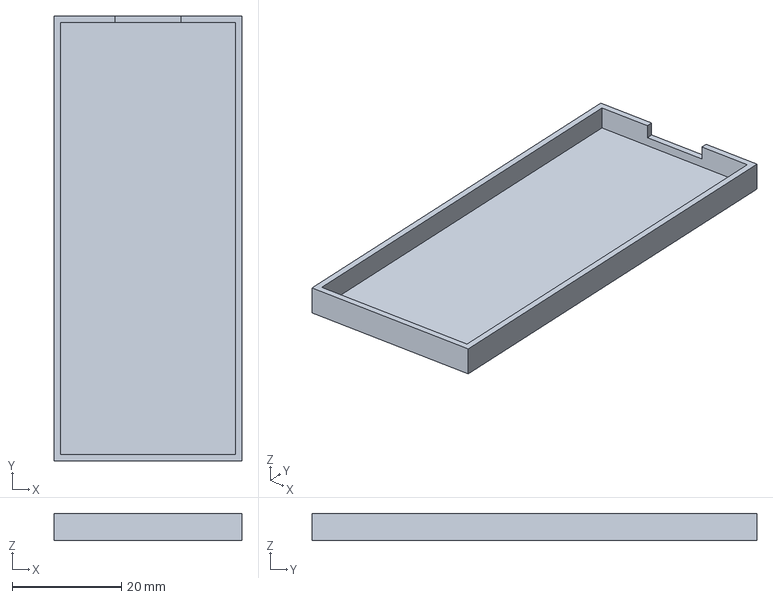
[picture p55: CAD file, 2026-09-20]
enclosure/harmony-r2-globtek/cad/battery-cage.step
34.4 x 81.4 x 5.00 mm
