dpaola2/Harmony/enclosure/harmony-r1/cad/fit-front.step

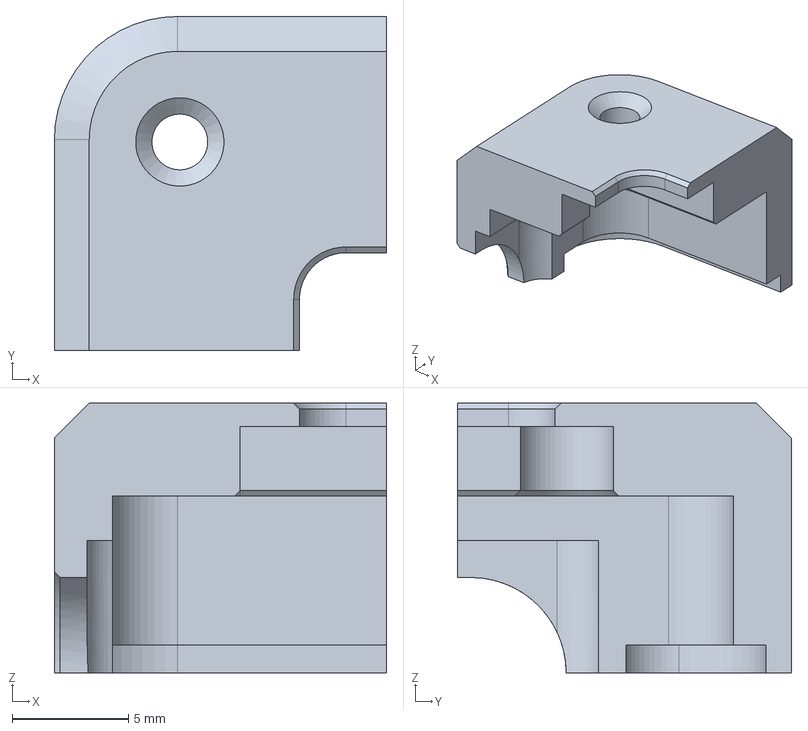
[picture p56: CAD file, 2026-09-20]
enclosure/harmony-r1/cad/fit-front.step
14.3 x 14.4 x 11.6 mm
