dpaola2/Harmony/enclosure/harmony-r2-globtek/cad/sd-caddy.step

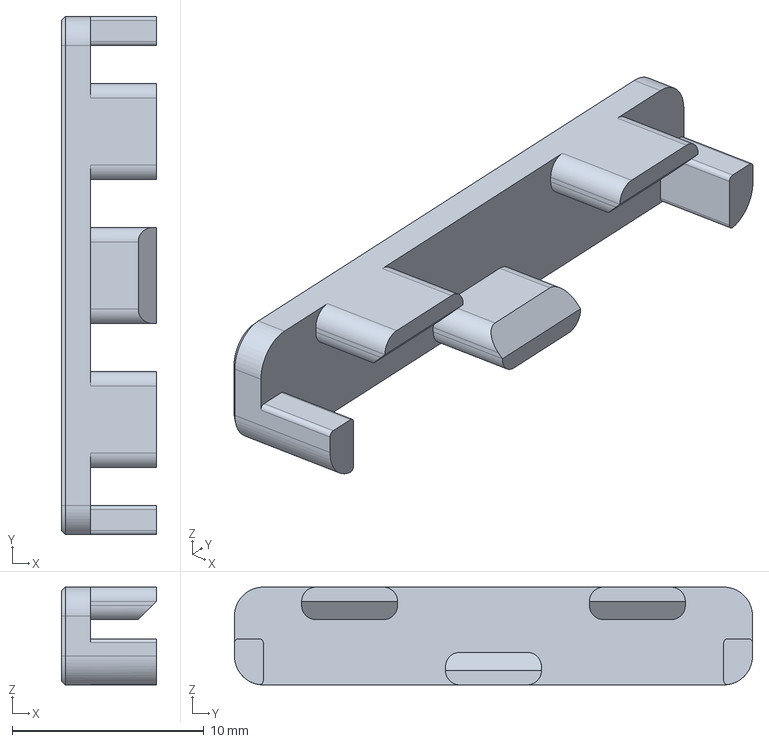
[picture p57: CAD file, 2026-09-20]
enclosure/harmony-r2-globtek/cad/sd-caddy.step
4.95 x 27.0 x 5.10 mm
