dpaola2/Harmony/enclosure/harmony-r1/cad/fit-back.step

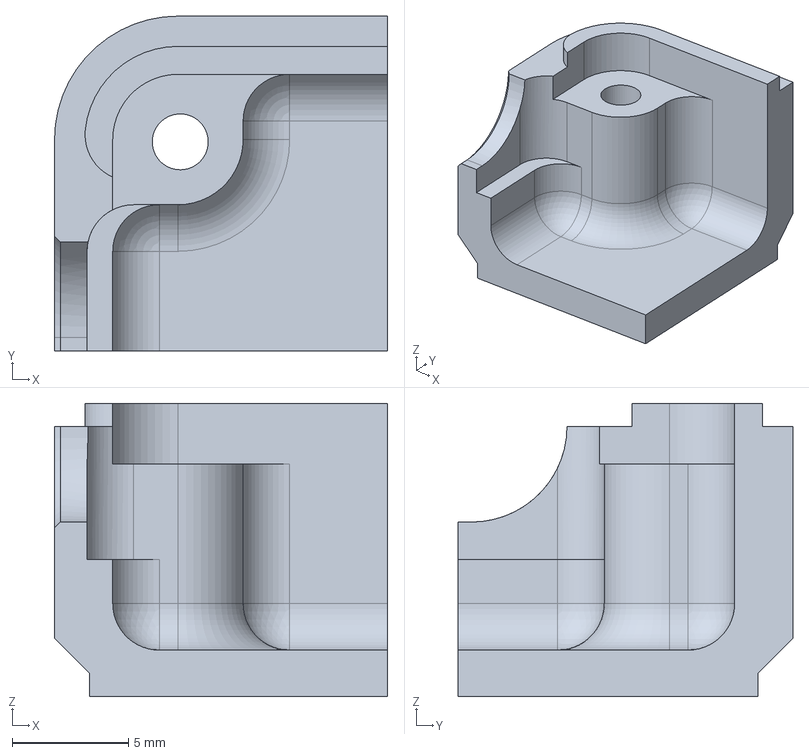
[picture p58: CAD file, 2026-09-20]
enclosure/harmony-r1/cad/fit-back.step
14.3 x 14.4 x 12.6 mm
