dpaola2/Harmony/enclosure/harmony-r1/preview/assembled.png

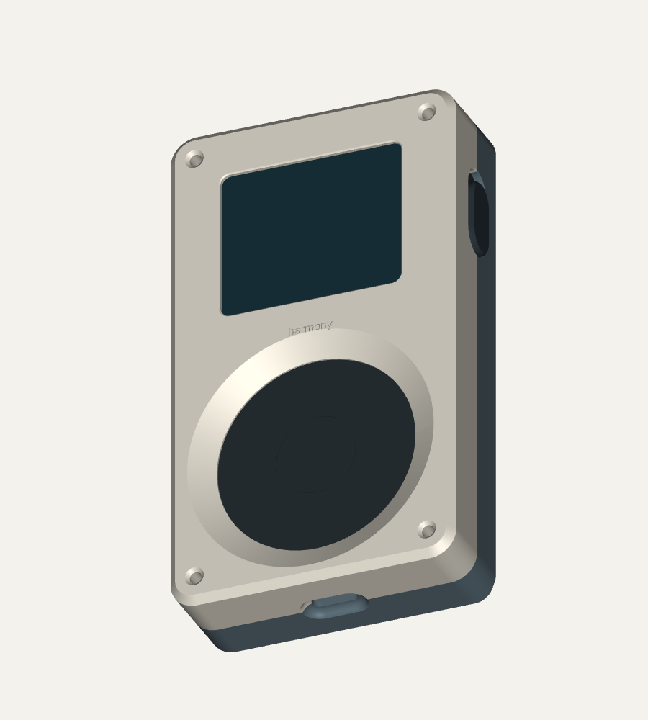
enclosure/harmony-r1/preview/assembled.png
