dpaola2/Harmony/hardware/revisions/harmony-r5-globtek-draft/README.md

# Harmony R5 GlobTek draft

U10 changed to MCP73871-1CCI/ML in schematic and PCB MPN property. Routed geometry and connectivity unchanged from R4. Local integration draft; not submitted or released. Temperature-sensor qualification remains open. See ../../procurement/globtek-integration/README.md.
