dpaola2/Harmony/firmware/mark-6/feather-carrier/components/bench_display/st7796_init.h

/* Initialization register values from Waveshare SKU 29318 vendor demo.
 * Source archive and SHA256: reference/waveshare-source.json.
 * Harmony portrait correction: MADCTL 0x48 (MX | BGR), rather than the
 * vendor demo 0x08. IMG_7717.HEIC showed horizontal mirroring with 0x08.
 * ST7796S datasheet section 9.2.28 defines MX as column address order.
 * Transport, bounds checks and renderer are the Harmony native driver.
 */
#pragma once
#include <stdint.h>
static const struct { uint8_t cmd, count; uint16_t delay_ms; uint8_t data[14]; } st7796_init[] = {
    {0x11, 0, 120, {0}},
    {0x36, 1, 0, {0x48}},
    {0x3a, 1, 0, {0x05}},
    {0xf0, 1, 0, {0xc3}},
    {0xf0, 1, 0, {0x96}},
    {0xb4, 1, 0, {0x01}},
    {0xb7, 1, 0, {0xc6}},
    {0xc0, 2, 0, {0x80, 0x45}},
    {0xc1, 1, 0, {0x13}},
    {0xc2, 1, 0, {0xa7}},
    {0xc5, 1, 0, {0x0a}},
    {0xe8, 8, 0, {0x40, 0x8a, 0x00, 0x00, 0x29, 0x19, 0xa5, 0x33}},
    {0xe0, 14, 0, {0xd0, 0x08, 0x0f, 0x06, 0x06, 0x33, 0x30, 0x33, 0x47, 0x17, 0x13, 0x13, 0x2b, 0x31}},
    {0xe1, 14, 0, {0xd0, 0x0a, 0x11, 0x0b, 0x09, 0x07, 0x2f, 0x33, 0x47, 0x38, 0x15, 0x16, 0x2c, 0x32}},
    {0xf0, 1, 0, {0x3c}},
    {0xf0, 1, 120, {0x69}},
    {0x21, 0, 0, {0}},
    {0x29, 0, 0, {0}},
};
