dpaola2/Harmony/firmware/mark-6/components/bench_display/panel_init.h

/* Init sequence adapted from pinned st7789py.py; see LICENSE-st7789. */
static const struct { uint8_t cmd, len, data[16]; unsigned delay_ms; } panel_init[] = {
    {0x11, 1, {0x00}, 120},
    {0x13, 1, {0x00}, 0},
    {0xb6, 2, {0x0a,0x82}, 0},
    {0x3a, 1, {0x55}, 10},
    {0xb2, 5, {0x0c,0x0c,0x00,0x33,0x33}, 0},
    {0xb7, 1, {0x35}, 0},
    {0xbb, 1, {0x28}, 0},
    {0xc0, 1, {0x0c}, 0},
    {0xc2, 2, {0x01,0xff}, 0},
    {0xc3, 1, {0x10}, 0},
    {0xc4, 1, {0x20}, 0},
    {0xc6, 1, {0x0f}, 0},
    {0xd0, 2, {0xa4,0xa1}, 0},
    {0xe0, 14, {0xd0,0x00,0x02,0x07,0x0a,0x28,0x32,0x44,0x42,0x06,0x0e,0x12,0x14,0x17}, 0},
    {0xe1, 14, {0xd0,0x00,0x02,0x07,0x0a,0x28,0x31,0x54,0x47,0x0e,0x1c,0x17,0x1b,0x1e}, 0},
    {0x21, 1, {0x00}, 0},
    {0x29, 1, {0x00}, 120},
};
