dpaola2/Harmony/firmware/mark-6/feather-carrier/components/carrier_board/carrier_pins.h

#pragma once
/* ESP32 GPIO numbers, NOT Feather header positions. Carrier Rev A only. */
#define CARRIER_SD_SCK 5
#define CARRIER_SD_MOSI 19
#define CARRIER_SD_MISO 21
#define CARRIER_SD_CS 25
#define CARRIER_TFT_SCK 14
#define CARRIER_TFT_MOSI 27
#define CARRIER_TFT_CS 26
#define CARRIER_TFT_DC 33
#define CARRIER_TFT_RST 32
#define CARRIER_TFT_LITE 4
#define CARRIER_I2C_SCL 20
#define CARRIER_I2C_SDA 22
#define CARRIER_PG 34
