dpaola2/Harmony/firmware/mark-6/feather-display-bench/main/trial_manifest.h

#pragma once
/* Expected SD inventory from verified September 26 trial manifest. */
static const struct {const char *path; size_t bytes;} expected_tracks[] = {
    {"Creed/Human Clay/01-01 Are You Ready.mp3",4563409},
    {"Creed/Human Clay/01-02 What If.mp3",5092956},
    {"Creed/Human Clay/01-03 Beautiful.mp3",4156730},
    {"Creed/Human Clay/01-04 Say I.mp3",5052830},
    {"Creed/Human Clay/01-05 Wrong Way.mp3",4152550},
    {"Creed/Human Clay/01-07 Never Die.mp3",4664968},
    {"Creed/Human Clay/01-08 With Arms Wide Open.mp3",4400828},
    {"Creed/Human Clay/01-09 Higher.mp3",5070386},
    {"Creed/Human Clay/01-10 Wash Away Those Years.mp3",5831505},
    {"Creed/Human Clay/01-11 Inside Us All.mp3",5582394},
    {"Creed/Human Clay/01-12 Young Grow Old.mp3",4587652},
    {"Radiohead/In Rainbows/01 15 Step.mp3",4679504},
    {"Radiohead/In Rainbows/02 Bodysnatchers.mp3",4419813},
    {"Radiohead/In Rainbows/03 Nude.mp3",5677443},
    {"Radiohead/In Rainbows/04 Weird Fishes - Arpeggi.mp3",6662151},
    {"Radiohead/In Rainbows/05 All I Need.mp3",4406750},
    {"Radiohead/In Rainbows/06 Faust Arp.mp3",2676247},
    {"Radiohead/In Rainbows/07 Reckoner.mp3",6794869},
    {"Radiohead/In Rainbows/08 House Of Cards.mp3",6719988},
    {"Radiohead/In Rainbows/09 Jigsaw Falling Into Place.mp3",5526763},
    {"Radiohead/In Rainbows/10 Videotape.mp3",5568125},
    {"The Head and The Heart/The Head and the Heart/01 Cats and Dogs.mp3",2774874},
    {"The Head and The Heart/The Head and the Heart/02 Coeur d'Alene.mp3",6276327},
    {"The Head and The Heart/The Head and the Heart/03 Ghosts.mp3",6209244},
    {"The Head and The Heart/The Head and the Heart/04 Down in the Valley.mp3",7286325},
    {"The Head and The Heart/The Head and the Heart/05 Rivers and Roads.mp3",6817375},
    {"The Head and The Heart/The Head and the Heart/06 Honey Come Home.mp3",4833114},
    {"The Head and The Heart/The Head and the Heart/07 Lost in My Mind.mp3",6220529},
    {"The Head and The Heart/The Head and the Heart/08 Winter Song.mp3",3937218},
    {"The Head and The Heart/The Head and the Heart/09 Sounds Like Hallelujah.mp3",4569172},
    {"The Head and The Heart/The Head and the Heart/10 Heaven Go Easy on Me.mp3",8170936},
    {"Third Eye Blind/Third Eye Blind/01-01 Losing A Whole Year.mp3",3216893},
    {"Third Eye Blind/Third Eye Blind/01-02 Narcolepsy.mp3",3662428},
    {"Third Eye Blind/Third Eye Blind/01-03 Semi-Charmed Life.mp3",4303978},
    {"Third Eye Blind/Third Eye Blind/01-04 Jumper.mp3",4372931},
    {"Third Eye Blind/Third Eye Blind/01-05 Graduate.mp3",3041339},
    {"Third Eye Blind/Third Eye Blind/01-06 How's It Going To Be.mp3",4063679},
    {"Third Eye Blind/Third Eye Blind/01-07 Thanks A Lot.mp3",4766260},
    {"Third Eye Blind/Third Eye Blind/01-08 Burning Man.mp3",2880845},
    {"Third Eye Blind/Third Eye Blind/01-09 Good For You.mp3",3715929},
    {"Third Eye Blind/Third Eye Blind/01-10 London.mp3",2996616},
    {"Third Eye Blind/Third Eye Blind/01-11 I Want You.mp3",4313600},
    {"Third Eye Blind/Third Eye Blind/01-12 The Background.mp3",4753307},
    {"Third Eye Blind/Third Eye Blind/01-13 Motorcycle Drive By.mp3",4206612},
    {"Third Eye Blind/Third Eye Blind/01-14 God Of Wine.mp3",5086417},
};
static const uint8_t expected_first_sha256[32] = {0x0a,0x10,0x19,0xa3,0xcf,0x01,0x9f,0x94,0x62,0xa4,0x77,0xf2,0xfd,0x97,0x7b,0x5e,0xc0,0xde,0x82,0xf4,0x70,0xe1,0xc0,0xfa,0x8e,0xc2,0x64,0x03,0xdd,0x0c,0xec,0x0a};
